HanYangZhao/TeensyMidiMerger/1.jpg

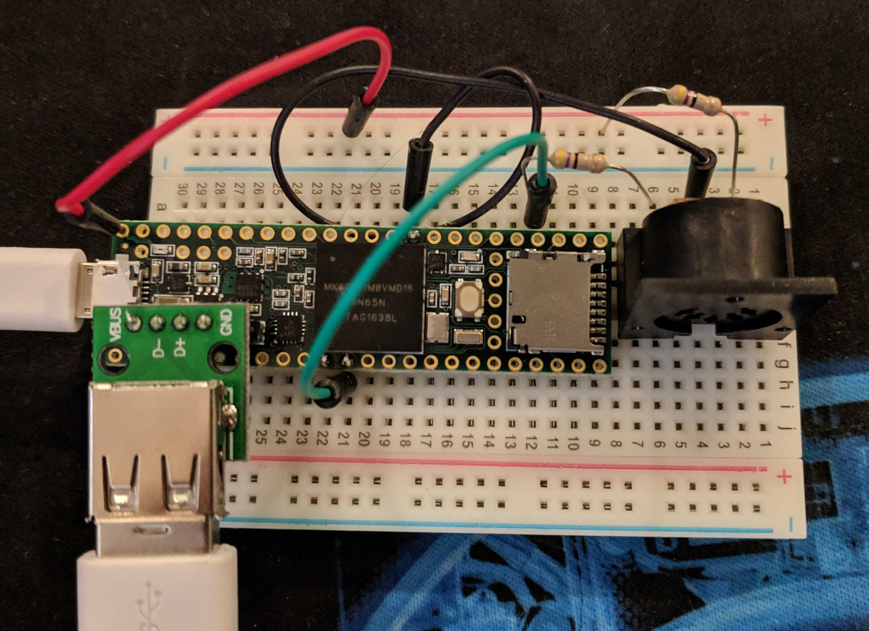
1.jpg
